muntedpissmole/sccs/kicad/1_wire_bus.kicad_sch

## KiCad design kicad/1_wire_bus.kicad_sch (2026-08-18)

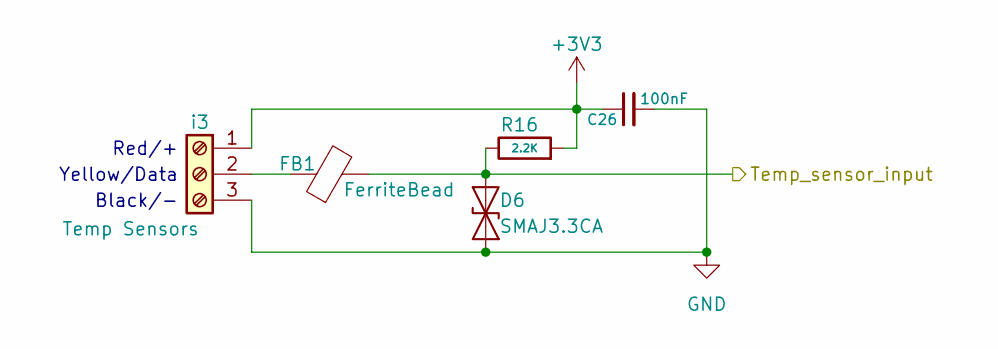
[picture p56: schematic 1_wire_bus.kicad_sch]

Parts:
C26: 100nF; C_0805_2012Metric; LCSC Part # C49678
D6: SMAJ3.3CA; D_SMA; LCSC Part # C18199545
FB1: FerriteBead; L_0603_1608Metric; LCSC Part # C1002
R16: 2.2K; R_0805_2012Metric; LCSC Part # C17520
i3: Temp Sensors; TerminalBlock_Phoenix_MKDS-1,5-3-5.08_1x03_P5.08mm_Horizont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; LCSC Part # C8412

Connections:
+3V3: C26.1, R16.2, i3.1
GND: C26.2, D6.1 (A1), i3.3
unnamed: FB1.1, i3.2
Temp_sensor_input: D6.2 (A2), FB1.2, R16.1

Notes on the sheet:
Yellow/Data
Red/+
Black/-
