muntedpissmole/sccs/kicad/SCCS-RPI.kicad_sch

## KiCad design kicad/SCCS-RPI.kicad_sch (2026-08-18)

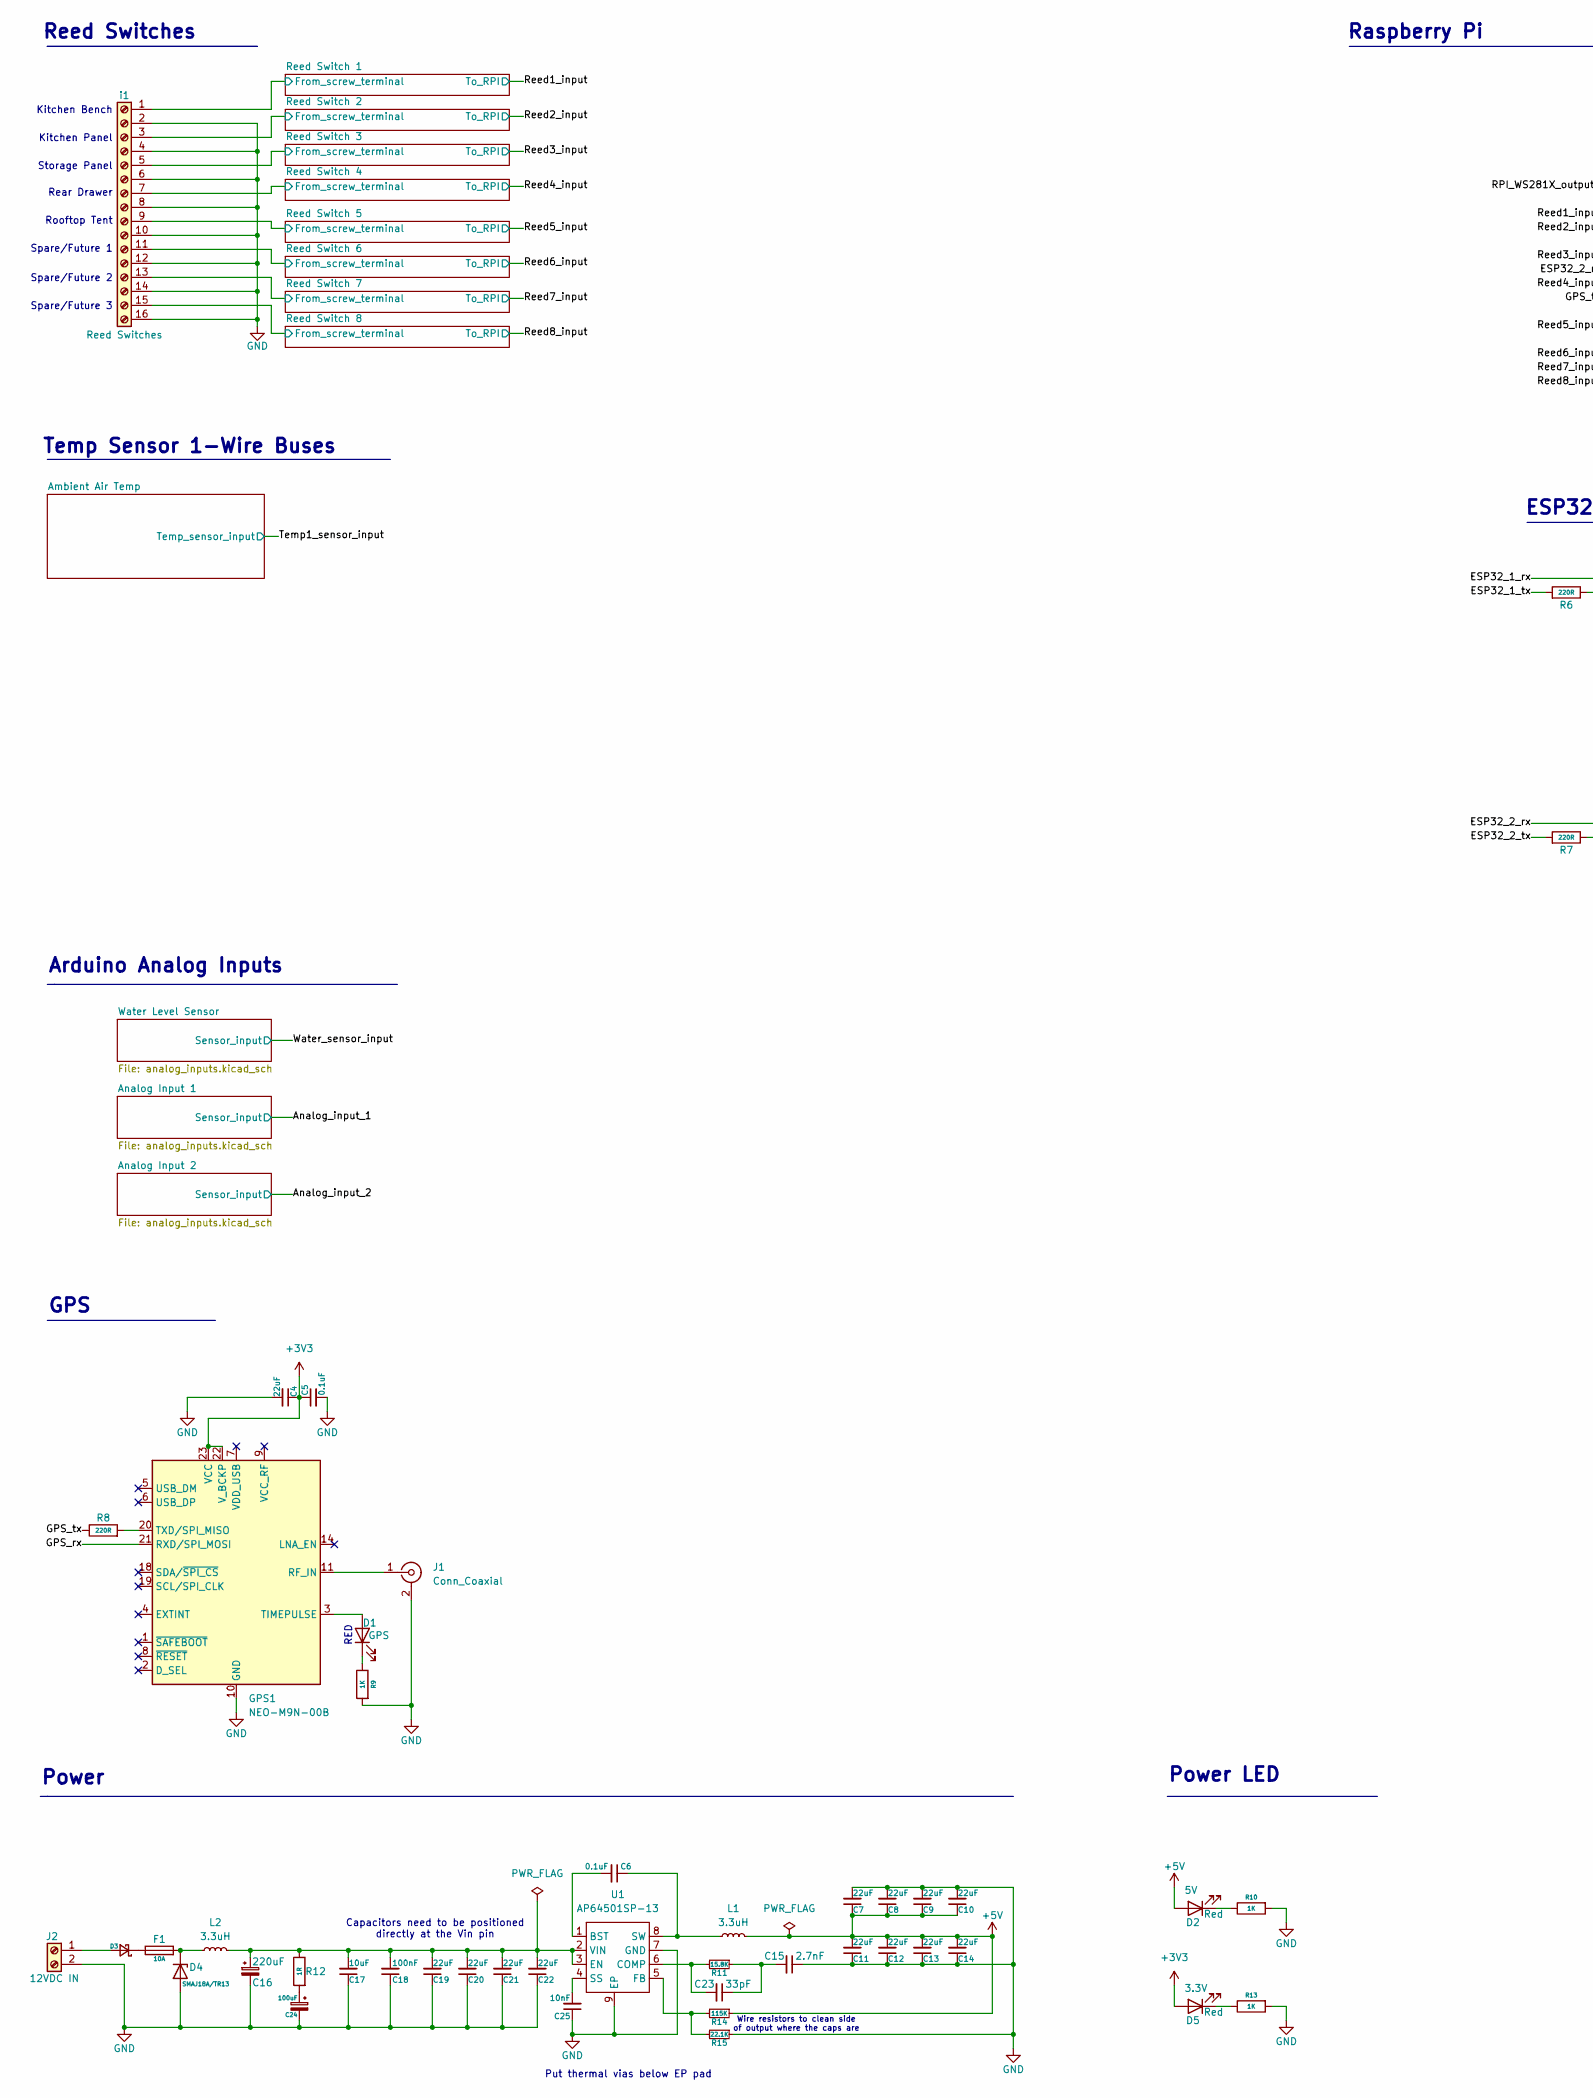
[picture p57: schematic SCCS-RPI.kicad_sch, part in row 1, column 1]

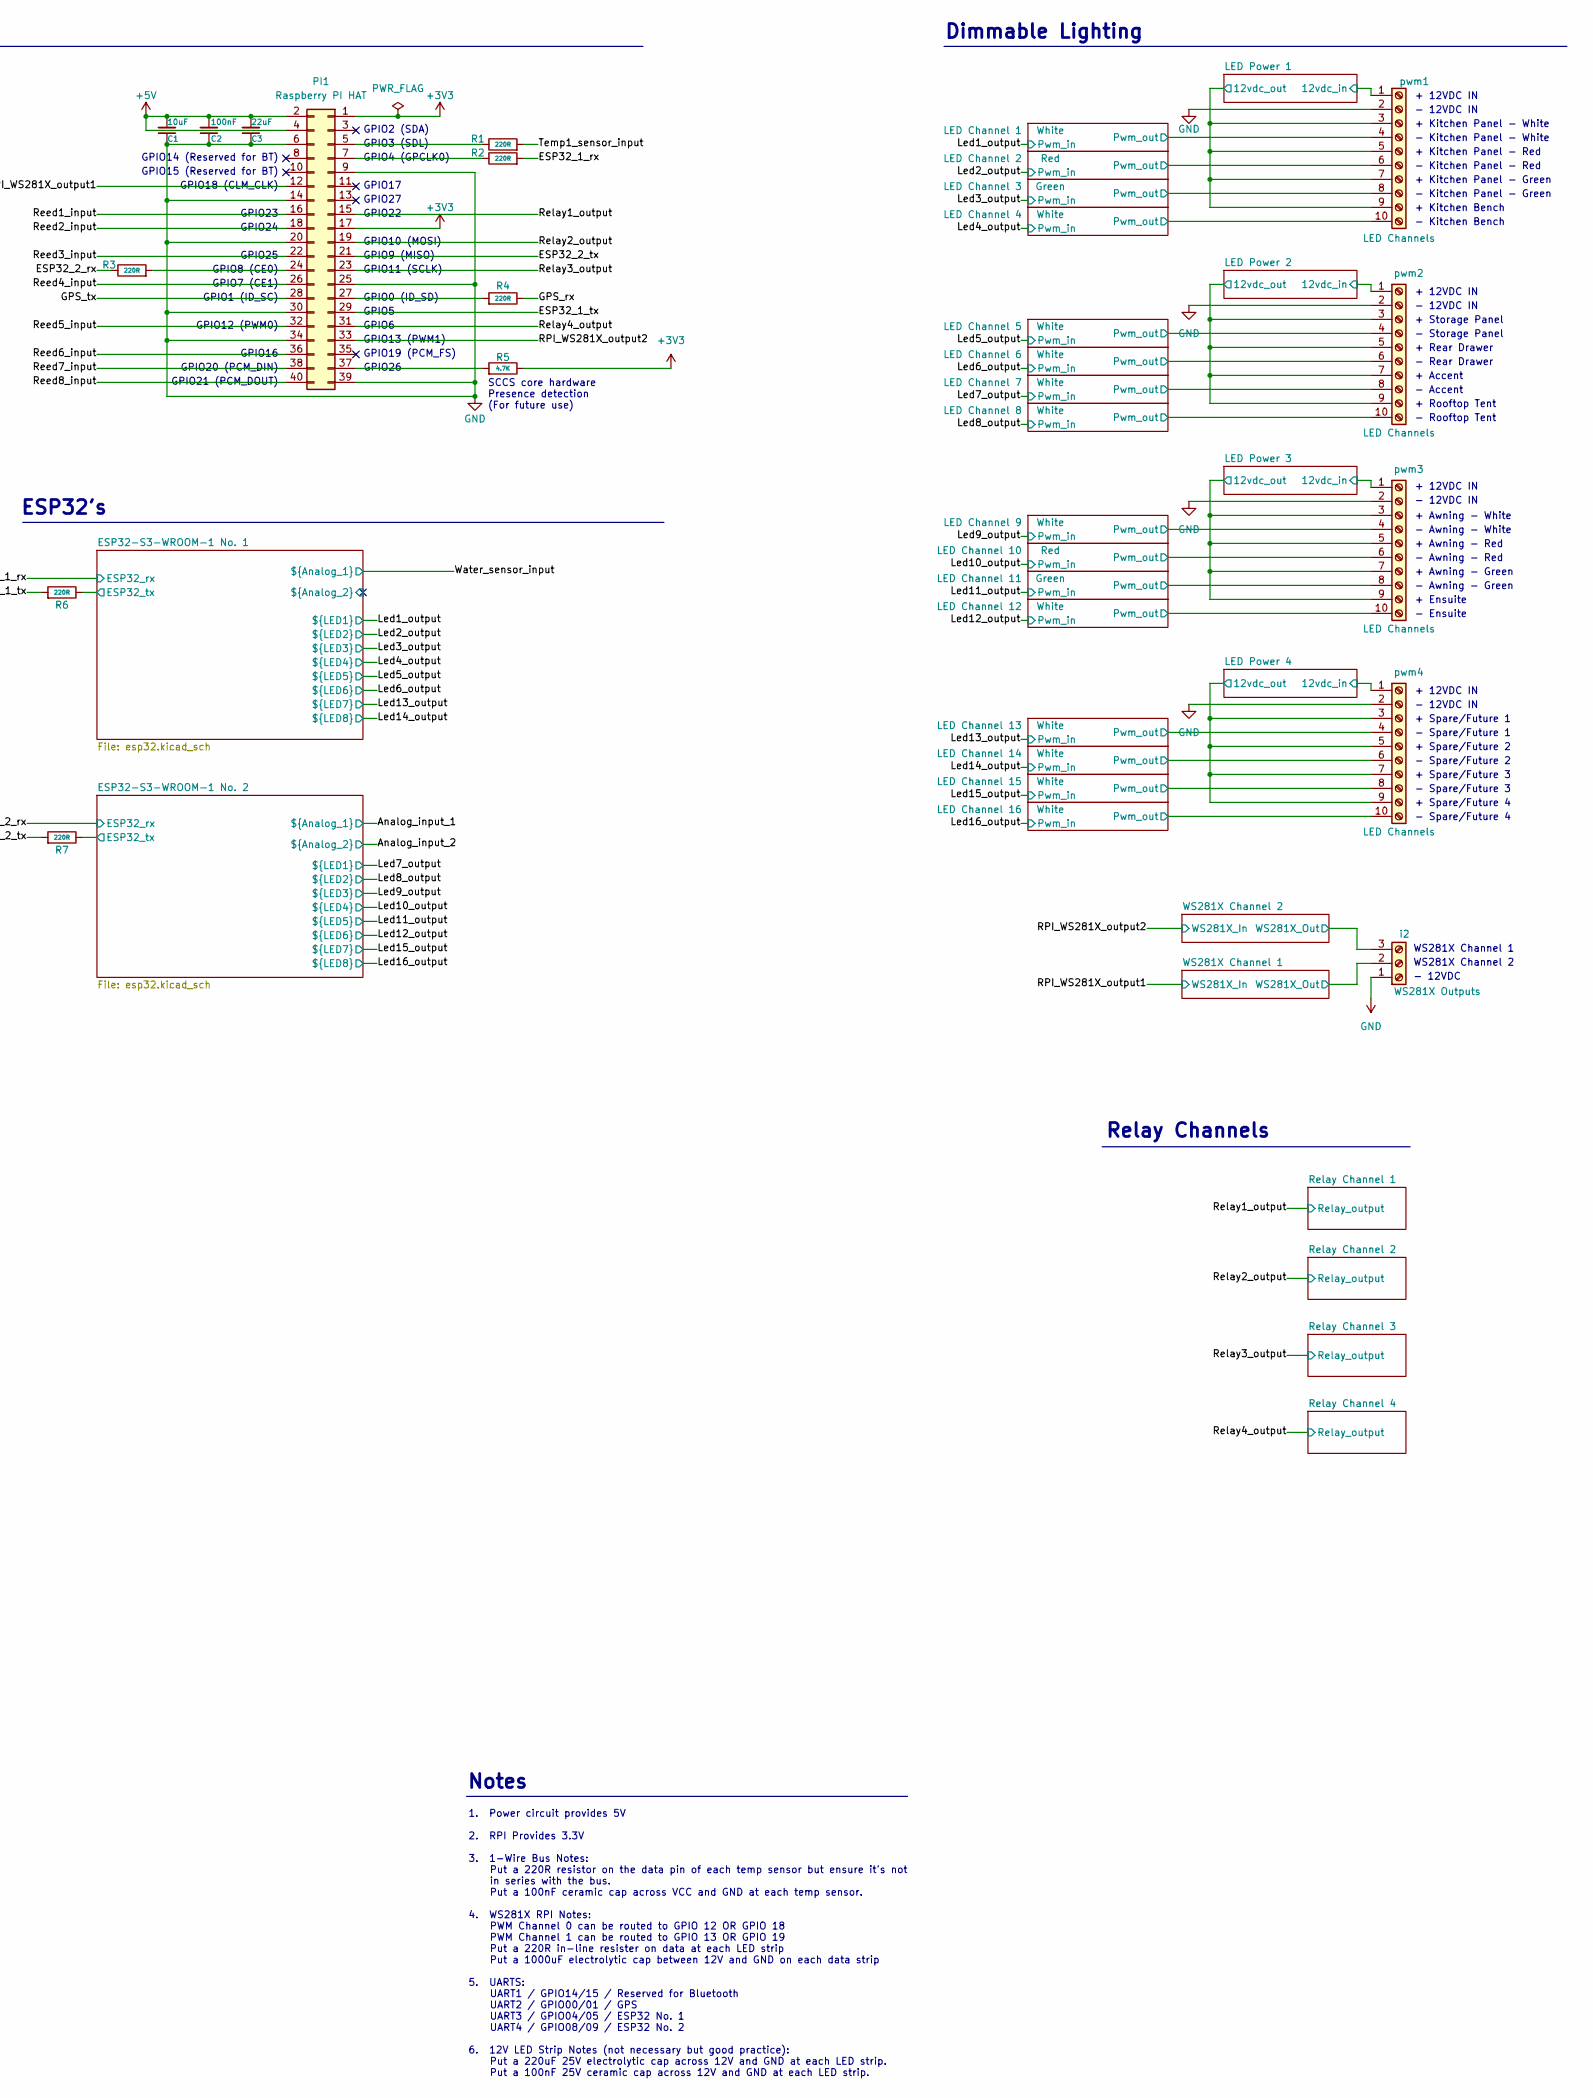
[picture p58: schematic SCCS-RPI.kicad_sch, part in row 1, column 2]

Parts:
C1, C17: 10uF; C_0805_2012Metric; LCSC Part # C15850
C2, C18: 100nF; C_0805_2012Metric; LCSC Part # C49678
C3, C4, C7, C8, C9, C10, C11, C12, C13, C14, C19, C20, C21, C22: 22uF; C_0805_2012Metric; LCSC Part # C86816
C5, C6: 0.1uF; C_0805_2012Metric; LCSC Part # C86041
C15: 2.7nF; C_0805_2012Metric; LCSC Part # C113859
C16: 220uF; CP_Elec_8x10; LCSC Part # C165536
C23: 33pF; C_0805_2012Metric; LCSC Part # C541516
C24: 100uF; CP_Radial_D6.3mm_P2.50mm; LCSC Part # C44587
C25: 10nF; C_0805_2012Metric; LCSC Part # C237168
D1: GPS; LED_0603_1608Metric; LCSC Part # C2286
D2: 5V; LED_0603_1608Metric; LCSC Part # C2286
D3: D_PowerDI-5; LCSC Part # C2759901
D4: SMAJ18A/TR13; D_SMB; LCSC Part # C571369
D5: 3.3V; LED_0603_1608Metric; LCSC Part # C2286
F1: 10A; Fuse_Bourns_MF-RG1000; LCSC Part # C14767
GPS1: NEO-M9N-00B; ublox_NEO; LCSC Part # C5119087
J1: Conn_Coaxial; SMA_Amphenol_132134-11_Vertical; LCSC Part # C20415804
J2: 12VDC IN; TerminalBlock_Phoenix_MKDS-1,5-2-5.08_1x02_P5.08mm_Horizont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; LCSC Part # C8445
L1, L2: 3.3uH; L_SXN_SMDRI127; LCSC Part # C24550
PI1: Raspberry PI HAT; PinSocket_2x20_P2.54mm_Vertical; LCSC Part # C132132
R1, R2, R3, R4, R6, R7, R8: 220R; R_0805_2012Metric; LCSC Part # C17557
R5: 4.7K; R_0805_2012Metric; LCSC Part # C17673
R9, R10, R13: 1K; R_0402_1005Metric; LCSC Part # C11702
R11: 15.8K; R_0805_2012Metric; LCSC Part # C17468
R12: 1R; R_0805_2012Metric; LCSC Part # C25271
R14: 115K; R_0805_2012Metric; LCSC Part # C158272
R15: 22.1K; R_0805_2012Metric; LCSC Part # C17552
U1: AP64501SP-13; SOIC-8-1EP_3.9x4.9mm_P1.27mm_EP2.95x4.9mm_Mask2.71x3.4mm_Th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; LCSC Part # C2071517
i1: Reed Switches; TerminalBlock_Phoenix_MKDS-1,5-16-5.08_1x16_P5.08mm_Horizon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; LCSC Part # C508906
i2: WS281X Outputs; TerminalBlock_Phoenix_MKDS-1,5-3-5.08_1x03_P5.08mm_Horizont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; LCSC Part # C8412
pwm1, pwm2, pwm3, pwm4: LED Channels; TerminalBlock_Phoenix_MKDS-1,5-10-5.08_1x10_P5.08mm_Horizon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; LCSC Part # C29173

Connections:
12vdc_in: pwm1.1, pwm2.1, pwm3.1, pwm4.1
12vdc_out: pwm1.3, pwm1.5, pwm1.7, pwm1.9, pwm2.3, pwm2.5, pwm2.7, pwm2.9, pwm3.3, pwm3.5, pwm3.7, pwm3.9, pwm4.3, pwm4.5, pwm4.7, pwm4.9
+3V3: C4.1, C5.1, D5.2 (A), GPS1.22 (V_BCKP), GPS1.23 (VCC), PI1.1, PI1.17, R5.1
+5V: C1.2, C2.2, C3.2, C7.1, C8.1, C9.1, C10.1, C11.2, C12.2, C13.2, C14.2, D2.2 (A), L1.2, PI1.2, PI1.4, R14.1
ESP32_1_rx: R2.2
ESP32_1_tx: PI1.29, R6.2
ESP32_2_rx: R3.1
ESP32_2_tx: PI1.21, R7.2
ESP32_tx: R6.1, R7.1
From_screw_terminal: i1.1, i1.3, i1.5, i1.7, i1.9, i1.11, i1.13, i1.15
GND: C1.1, C2.1, C3.1, C4.2, C5.2, C7.2, C8.2, C9.2, C10.2, C11.1, C12.1, C13.1, C14.1, C15.1, C16.2, C17.1, C18.1, C19.1, C20.1, C21.1, C22.1, C24.2, C25.1, D4.2 (A), GPS1.10 (GND), GPS1.12 (GND), GPS1.13 (GND), GPS1.24 (GND), J1.2 (Ext), J2.2, PI1.6, PI1.9, PI1.14, PI1.20, PI1.25, PI1.30, PI1.34, PI1.39, R9.2, R10.2, R13.2, R15.1, U1.7 (GND), U1.9 (EP), i1.2, i1.4, i1.6, i1.8, i1.10, i1.12, i1.14, i1.16, i2.1, pwm1.2, pwm2.2, pwm3.2, pwm4.2
GPS_rx: GPS1.21 (RXD/SPI_MOSI), R4.1
GPS_tx: PI1.28, R8.1
unnamed: C6.1, L1.1, U1.8 (SW)
unnamed: C6.2, U1.1 (BST)
unnamed: C15.2, C23.1, R11.1
unnamed: C16.1, C17.2, C18.2, C19.2, C20.2, C21.2, C22.2, L2.2, R12.1, U1.2 (VIN), U1.3 (EN)
unnamed: C23.2, R11.2, U1.6 (COMP)
unnamed: C24.1, R12.2
unnamed: C25.2, U1.4 (SS)
unnamed: D1.1 (K), R9.1
unnamed: D1.2 (A), GPS1.3 (TIMEPULSE)
unnamed: D2.1 (K), R10.1
unnamed: D3.1 (K), F1.1
unnamed: D3.2 (A), J2.1
unnamed: D4.1 (K), F1.2, L2.1
unnamed: D5.1 (K), R13.1
unnamed: GPS1.11 (RF_IN), J1.1 (In)
unnamed: GPS1.20 (TXD/SPI_MISO), R8.2
unnamed: PI1.5, R1.1
unnamed: PI1.7, R2.1
unnamed: PI1.24, R3.2
unnamed: PI1.27, R4.2
unnamed: PI1.37, R5.2
unnamed: R14.2, R15.2, U1.5 (FB)
Pwm_out: pwm1.4, pwm1.6, pwm1.8, pwm1.10, pwm2.4, pwm2.6, pwm2.8, pwm2.10, pwm3.4, pwm3.6, pwm3.8, pwm3.10, pwm4.4, pwm4.6, pwm4.8, pwm4.10
RPI_WS281X_output1: PI1.12
RPI_WS281X_output2: PI1.33
Reed1_input: PI1.16
Reed2_input: PI1.18
Reed3_input: PI1.22
Reed4_input: PI1.26
Reed5_input: PI1.32
Reed6_input: PI1.36
Reed7_input: PI1.38
Reed8_input: PI1.40
Relay1_output: PI1.15
Relay2_output: PI1.19
Relay3_output: PI1.23
Relay4_output: PI1.31
Temp1_sensor_input: R1.2
WS281X_Out: i2.2, i2.3

Notes on the sheet:
+ Awning - White
- Spare/Future 3
GPIO1 (ID_SC)
Capacitors need to be positioned directly at the Vin pin
+ Spare/Future 1
Put thermal vias below EP pad
WS281X Channel 1
GPIO12 (PWM0)
Rooftop Tent
Temp Sensor 1-Wire Buses
GPIO15 (Reserved for BT)
- 12VDC IN
SCCS core hardware Presence detection (For future use)
GPIO22
GPIO23
- Kitchen Panel - Red
Spare/Future 3
GPIO20 (PCM_DIN)
1. Power circuit provides 5V 2. RPI Provides 3.3V 3. 1-Wire Bus Notes: Put a 220R resistor on the data pin of each temp sensor but ensure it's not in series with the bus. Put a 100nF ceramic cap across VCC and GND at each temp sensor. 4. WS281X RPI Notes: PWM Channel 0 can be routed to GPIO 12 OR G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
- Rear Drawer
ESP32's
+ Kitchen Bench
- Accent
GPIO25
GPIO27
+ 12VDC IN
GPIO11 (SCLK)
+ Storage Panel
+ Ensuite
- Kitchen Bench
GPIO7 (CE1)
Kitchen Bench
Notes
- Spare/Future 1
GPS
GPIO4 (GPCLK0)
- Rooftop Tent
Spare/Future 2
GPIO3 (SDL)
+ Awning - Green
+ Spare/Future 2
GPIO6
GPIO5
GPIO18 (CLM_CLK)
GPIO21 (PCM_DOUT)
Rear Drawer
GPIO13 (PWM1)
+ Rooftop Tent
+ Spare/Future 4
Spare/Future 1
+ Kitchen Panel - Red
Raspberry Pi
+ Accent
GPIO0 (ID_SD)
+ Kitchen Panel - White
+ Awning - Red
+ Kitchen Panel - Green
RED
GPIO9 (MISO)
GPIO17
- 12VDC
- Kitchen Panel - Green
GPIO16
GPIO14 (Reserved for BT)
+ Rear Drawer
GPIO24
Reed Switches
GPIO26
Power
- Storage Panel
- Awning - Red
Wire resistors to clean side of output where the caps are
- Awning - Green
- Spare/Future 2
Arduino Analog Inputs
- Spare/Future 4
- Kitchen Panel - White
Relay Channels
- Awning - White
Power LED
GPIO8 (CE0)
GPIO10 (MOSI)
Kitchen Panel
Dimmable Lighting
- Ensuite
Storage Panel
GPIO19 (PCM_FS)
GPIO2 (SDA)
WS281X Channel 2
+ Spare/Future 3
