muntedpissmole/sccs/kicad/led_channel.kicad_sch

## KiCad design kicad/led_channel.kicad_sch (2026-08-18)

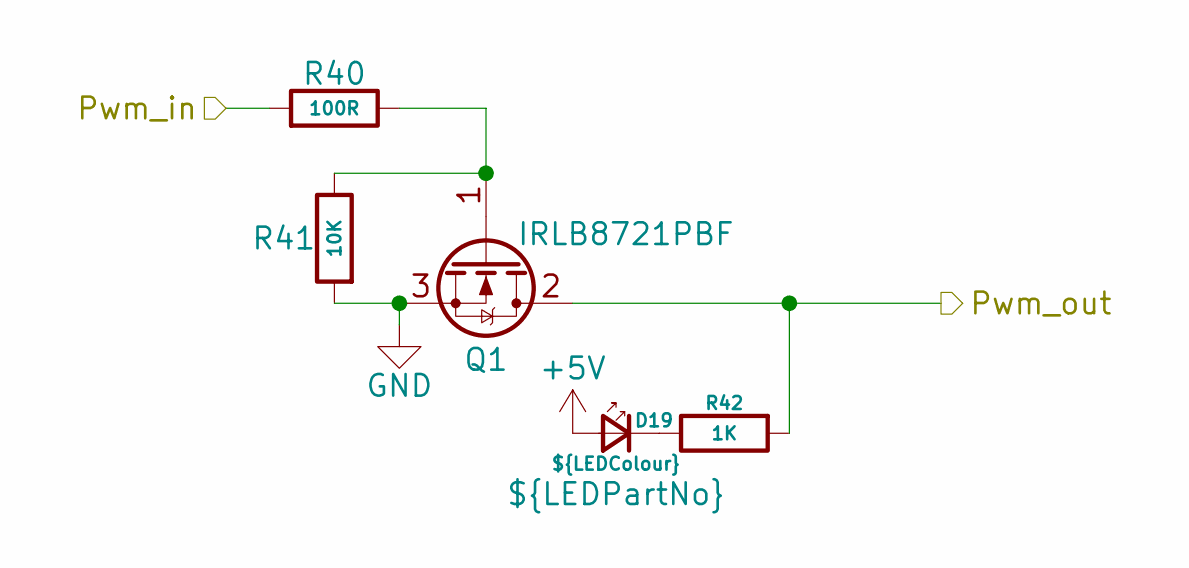
[picture p61: schematic led_channel.kicad_sch]

Parts:
D19: ${LEDColour}; LED_0603_1608Metric; LCSC Part # ${LEDPartNo}
Q1: IRLB8721PBF; TO-252-2; LCSC Part # C99124
R40: 100R; R_0805_2012Metric; LCSC Part # C17408
R41: 10K; R_0805_2012Metric; LCSC Part # C17414
R42: 1K; R_0805_2012Metric; LCSC Part # C17513

Connections:
+5V: D19.2 (A)
GND: Q1.3 (S), R41.2
unnamed: D19.1 (K), R42.1
unnamed: Q1.1 (G), R40.1, R41.1
Pwm_in: R40.2
Pwm_out: Q1.2 (D), R42.2
