muntedpissmole/sccs/kicad/relay_channel.kicad_sch

## KiCad design kicad/relay_channel.kicad_sch (2026-08-18)

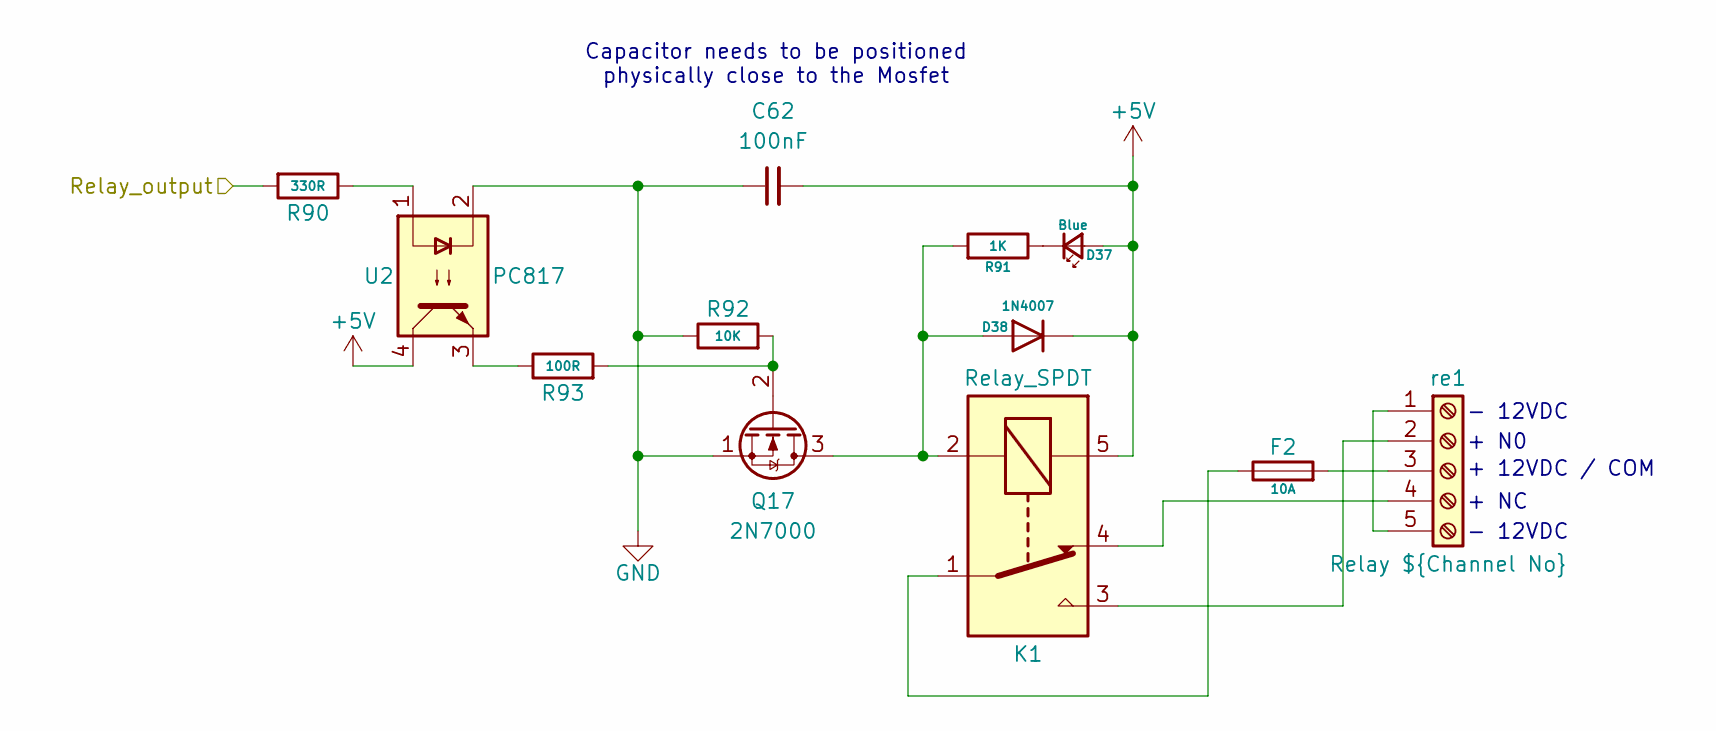
[picture p64: schematic relay_channel.kicad_sch]

Parts:
C62: 100nF; C_0805_2012Metric; LCSC Part # C49678
D37: Blue; LED_0603_1608Metric; LCSC Part # C2288
D38: 1N4007; D_SMA; LCSC Part # C64915
F2: 10A; Fuse_Bourns_MF-RG1000; LCSC Part # C14767
K1: Relay_SPDT; Relay_SPDT_SANYOU_SRD_Series_Form_C; LCSC Part # C35449
Q17: 2N7000; TO-92_Inline; LCSC Part # C9114
R90: 330R; R_0805_2012Metric; LCSC Part # C17630
R91: 1K; R_0603_1608Metric; LCSC Part # C5123612
R92: 10K; R_0805_2012Metric; LCSC Part # C17414
R93: 100R; R_0805_2012Metric; LCSC Part # C17408
U2: PC817; DIP-4_W7.62mm; LCSC Part # C5353
re1: Relay ${Channel No}; TerminalBlock_Phoenix_MKDS-3-5-5.08_1x05_P5.08mm_Horizontal; LCSC Part # C8423

Connections:
+5V: C62.2, D37.2 (A), D38.1 (K), K1.5, U2.4
GND: C62.1, Q17.1 (S), R92.1, U2.2
unnamed: D37.1 (K), R91.1
unnamed: D38.2 (A), K1.2, Q17.3 (D), R91.2
unnamed: F2.1, K1.1
unnamed: F2.2, re1.3
unnamed: K1.3, re1.2
unnamed: K1.4, re1.4
unnamed: Q17.2 (G), R92.2, R93.2
unnamed: R90.1, U2.1
unnamed: R93.1, U2.3
unnamed: re1.1, re1.5
Relay_output: R90.2

Notes on the sheet:
+ NC
+ N0
+ 12VDC / COM
- 12VDC
Capacitor needs to be positioned physically close to the Mosfet
