muntedpissmole/sccs/kicad/ws2815.kicad_sch

## KiCad design kicad/ws2815.kicad_sch (2026-08-18)

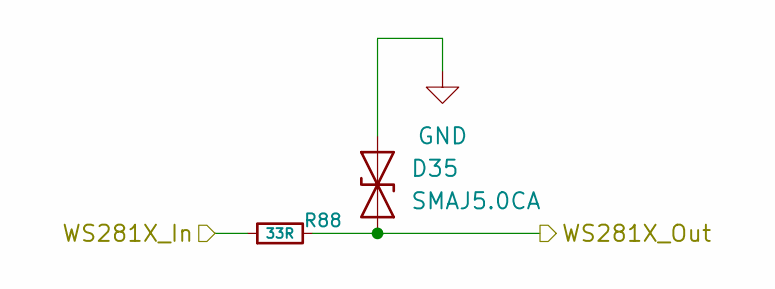
[picture p65: schematic ws2815.kicad_sch]

Parts:
D35: SMAJ5.0CA; D_SMA; LCSC Part # C78402
R88: 33R; R_0805_2012Metric; LCSC Part # C17634

Connections:
GND: D35.1 (A1)
WS281X_In: R88.1
WS281X_Out: D35.2 (A2), R88.2
