muntedpissmole/sccs/engine/world.py

from __future__ import annotations

import threading
import time
from dataclasses import dataclass, field
from typing import Dict, List, Optional

from .intent import IntentExpiry, LightIntent, RelayIntent


@dataclass
class WorldState:
    reeds: Dict[str, bool] = field(default_factory=dict)
    reed_forces: Dict[str, bool] = field(default_factory=dict)
    phase: str = ""
    phase_forced: Optional[str] = None
    light_intents: Dict[str, LightIntent] = field(default_factory=dict)
    relay_intents: Dict[str, RelayIntent] = field(default_factory=dict)
    active_scene: Optional[str] = None
    last_scene: Optional[str] = None
    observed_lights: Dict[str, int] = field(default_factory=dict)
    observed_light_modes: Dict[str, str] = field(default_factory=dict)
    observed_relays: Dict[str, bool] = field(default_factory=dict)
    observed_screens: Dict[str, bool] = field(default_factory=dict)


class WorldStore:
    """Thread-safe canonical world model. Inputs write; policy reads."""

    def __init__(self, reed_names: List[str], light_names: List[str], relay_names: List[str]):
        self._lock = threading.RLock()
        self._state = WorldState(
            reeds={n: True for n in reed_names},
            observed_lights={n: 0 for n in light_names},
            observed_relays={n: False for n in relay_names},
        )
        self._light_to_reed: Dict[str, str] = {}

    def set_light_to_reed_map(self, mapping: Dict[str, str]):
        self._light_to_reed = dict(mapping)

    def snapshot(self) -> WorldState:
        with self._lock:
            import copy
            return copy.deepcopy(self._state)

    def update_reeds(self, reeds: Dict[str, bool], *, transition_reeds: Optional[List[str]] = None):
        """Update reed raw state. Clear slider intents for lights linked to any transitioned reed."""
        with self._lock:
            transition_reeds = transition_reeds or []
            self._state.reeds = dict(reeds)
            if transition_reeds:
                self._invalidate_intents_for_reed_transition(transition_reeds)

    def set_reed_force(self, reed: str, closed: Optional[bool]):
        with self._lock:
            if closed is None:
                self._state.reed_forces.pop(reed, None)
            else:
                self._state.reed_forces[reed] = closed
            self._invalidate_scene_selection()

    def clear_all_reed_forces(self):
        with self._lock:
            self._state.reed_forces.clear()
            self._invalidate_scene_selection()

    def set_phase(self, phase: str, forced: Optional[str] = None, *, invalidate: bool = False):
        with self._lock:
            self._state.phase = phase
            self._state.phase_forced = forced
            if invalidate:
                self._invalidate_intents_for_phase_change()

    def set_light_intent(
        self,
        light: str,
        brightness: int,
        mode: Optional[str] = None,
        expires: IntentExpiry = "until_reed_close",
    ):
        with self._lock:
            self._state.light_intents[light] = LightIntent(
                brightness=brightness, mode=mode, expires=expires, set_at=time.time()
            )
            self._invalidate_scene_selection()

    def clear_light_intent(self, light: str):
        with self._lock:
            self._state.light_intents.pop(light, None)

    def clear_all_light_intents(self):
        with self._lock:
            self._state.light_intents.clear()

    def clear_light_intents_for_reeds(self, reeds):
        """Clear slider intents only for lights linked to the given reeds."""
        target = set(reeds)
        with self._lock:
            for light in list(self._state.light_intents.keys()):
                reed = self._light_to_reed.get(light)
                if reed and reed in target:
                    del self._state.light_intents[light]

    def clear_active_scene(self):
        with self._lock:
            self._state.active_scene = None

    def clear_last_scene(self):
        with self._lock:
            self._state.last_scene = None

    def set_relay_intent(self, relay: str, on: bool, expires: IntentExpiry = "manual"):
        with self._lock:
            self._state.relay_intents[relay] = RelayIntent(on=on, expires=expires, set_at=time.time())

    def set_active_scene(self, scene: Optional[str]):
        with self._lock:
            self._state.active_scene = scene
            if scene:
                self._state.last_scene = scene
                for light in list(self._state.light_intents.keys()):
                    intent = self._state.light_intents[light]
                    if intent.expires == "until_scene_clear":
                        del self._state.light_intents[light]

    def update_observed_lights(self, lights: Dict[str, int], modes: Optional[Dict[str, str]] = None):
        with self._lock:
            self._state.observed_lights.update(lights)
            if modes:
                self._state.observed_light_modes.update(modes)

    def seed_observed_light(self, name: str, brightness: int, mode: Optional[str] = None):
        """Optimistic observed level while a ramp is in flight (replaced on next hardware read)."""
        with self._lock:
            self._state.observed_lights[name] = brightness
            if mode is not None:
                self._state.observed_light_modes[name] = mode

    def clear_observed_lights(self, lights) -> None:
        """Drop cached hardware reads so reconcile won't trust stale levels."""
        with self._lock:
            for light in lights:
                self._state.observed_lights.pop(light, None)
                self._state.observed_light_modes.pop(light, None)

    def update_observed_relays(self, relays: Dict[str, bool]):
        with self._lock:
            self._state.observed_relays.update(relays)

    def update_observed_screens(self, screens: Dict[str, bool]):
        with self._lock:
            self._state.observed_screens.update(screens)

    def _invalidate_intents_for_reed_transition(self, transitioned_reeds: List[str]):
        transitioned = set(transitioned_reeds)
        for light in list(self._state.light_intents.keys()):
            reed = self._light_to_reed.get(light)
            if reed and reed in transitioned:
                del self._state.light_intents[light]
        self._invalidate_scene_selection()

    def _invalidate_intents_for_phase_change(self):
        self._state.light_intents.clear()
        self._invalidate_scene_selection()

    def _invalidate_scene_selection(self):
        """Drop active scene on phase change, reed event, or manual slider."""
        self._state.active_scene = None
        self._state.last_scene = None
